Taro-Hayashi/Kombucha2/img/elecrow.png

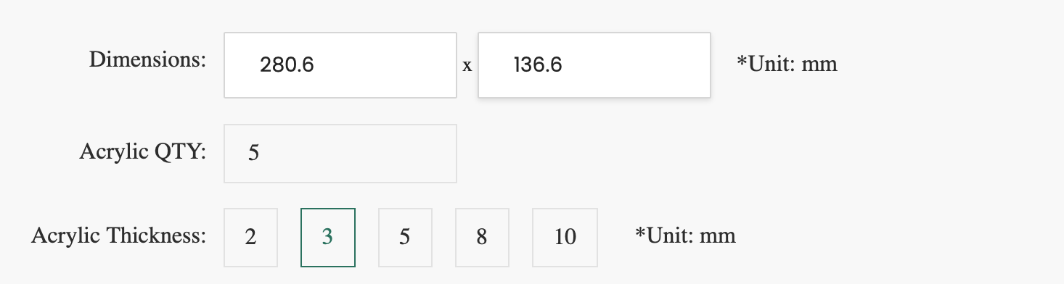
img/elecrow.png
