Taro-Hayashi/Kombucha2/img/IMG_2246.jpeg

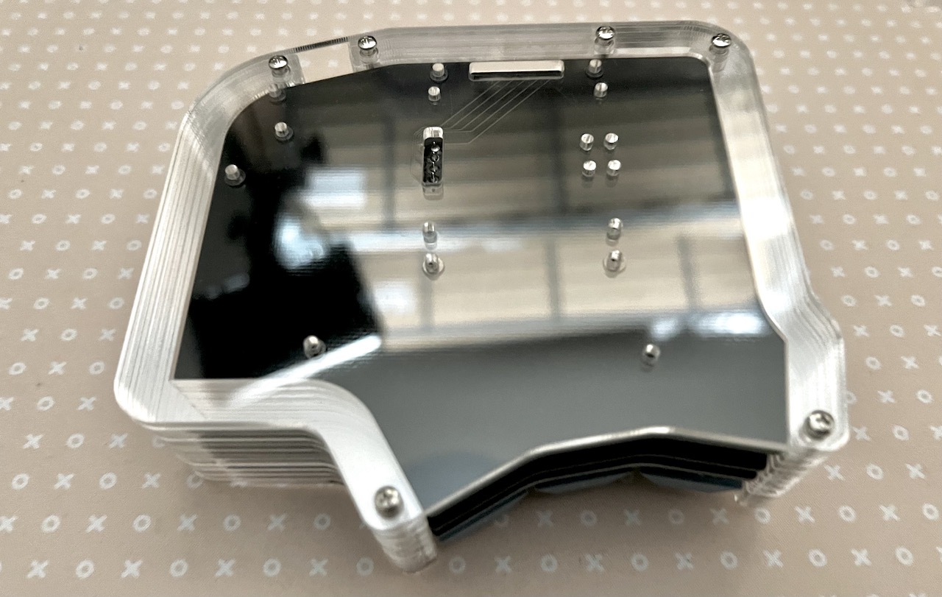
img/IMG_2246.jpeg
