Taro-Hayashi/Kombucha2/img/IMG_2586.jpeg

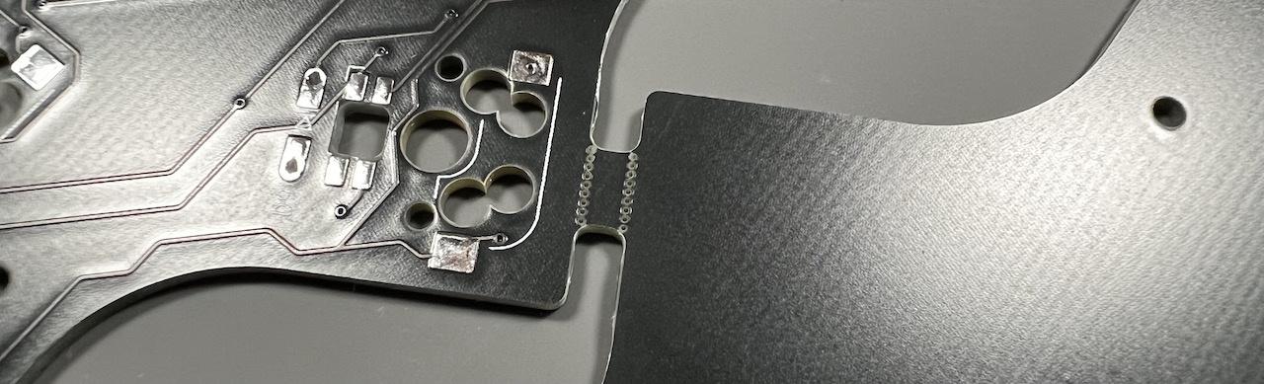
img/IMG_2586.jpeg
