Taro-Hayashi/Kombucha2/img/IMG_2591.jpeg

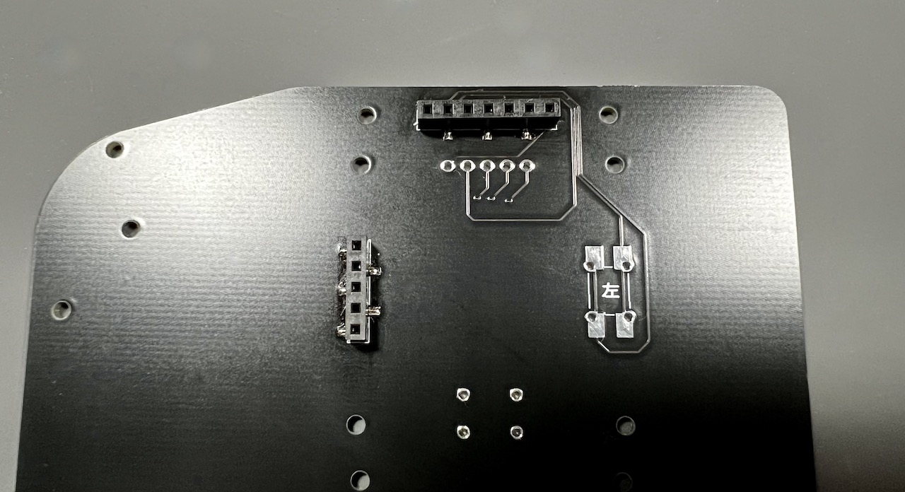
img/IMG_2591.jpeg
