Taro-Hayashi/Kombucha2/img/IMG_2621.jpeg

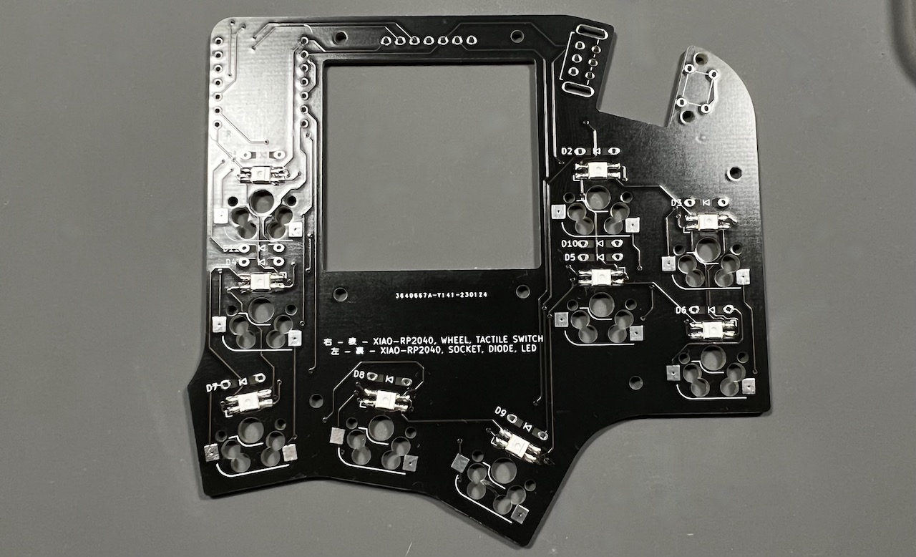
img/IMG_2621.jpeg
