Taro-Hayashi/Kombucha2/img/IMG_2639.jpeg

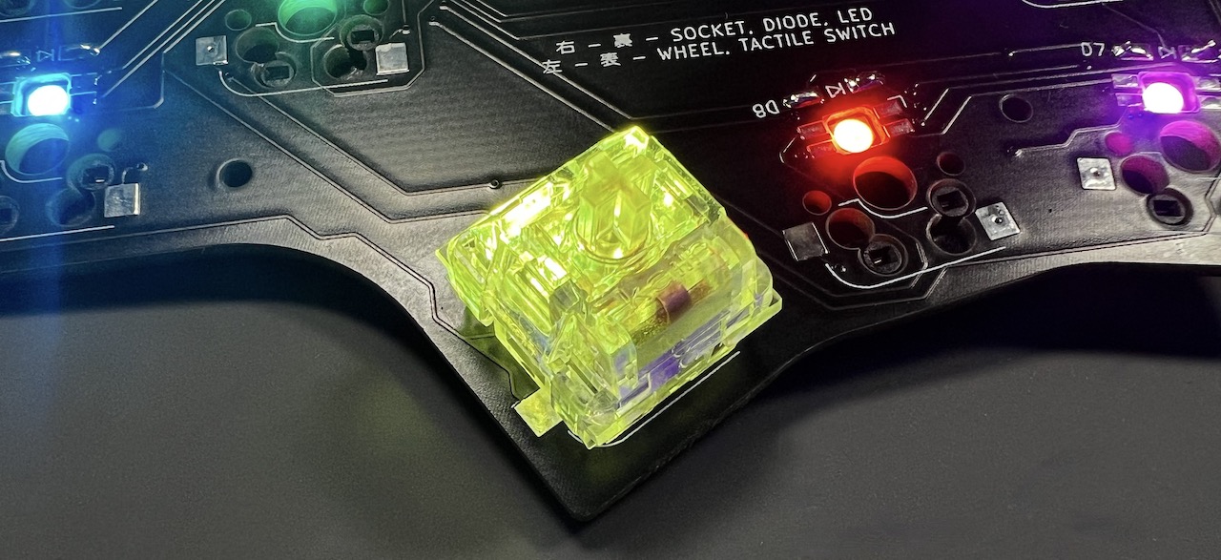
img/IMG_2639.jpeg
