Taro-Hayashi/Kombucha2/img/IMG_2836.jpg

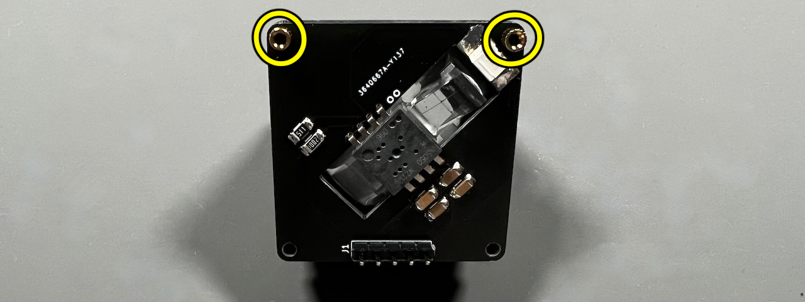
img/IMG_2836.jpg
