Taro-Hayashi/Kombucha2/img/IMG_2845.jpeg

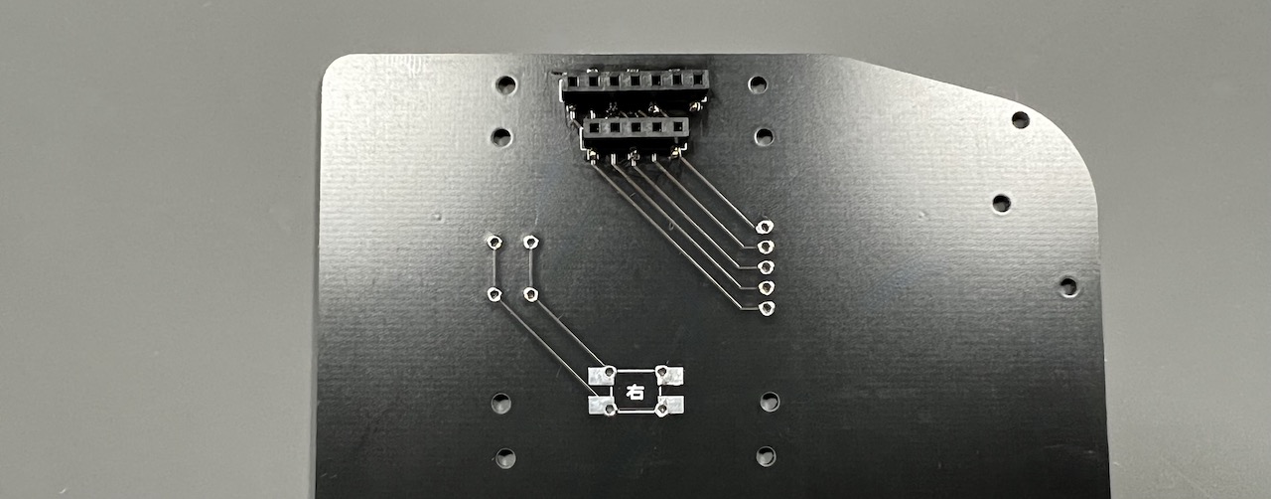
img/IMG_2845.jpeg
