Taro-Hayashi/Kombucha2/img/IMG_2849.jpeg

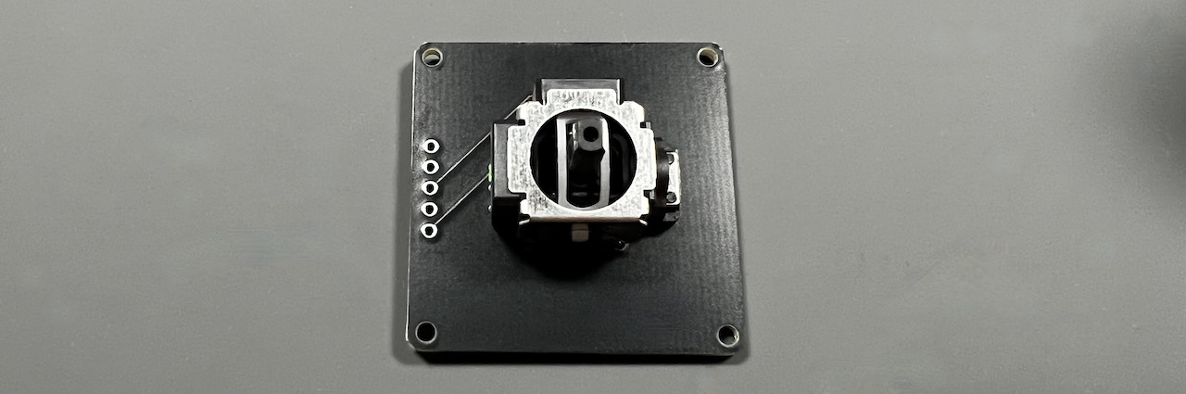
img/IMG_2849.jpeg
