Taro-Hayashi/Kombucha2/img/IMG_2858.jpeg

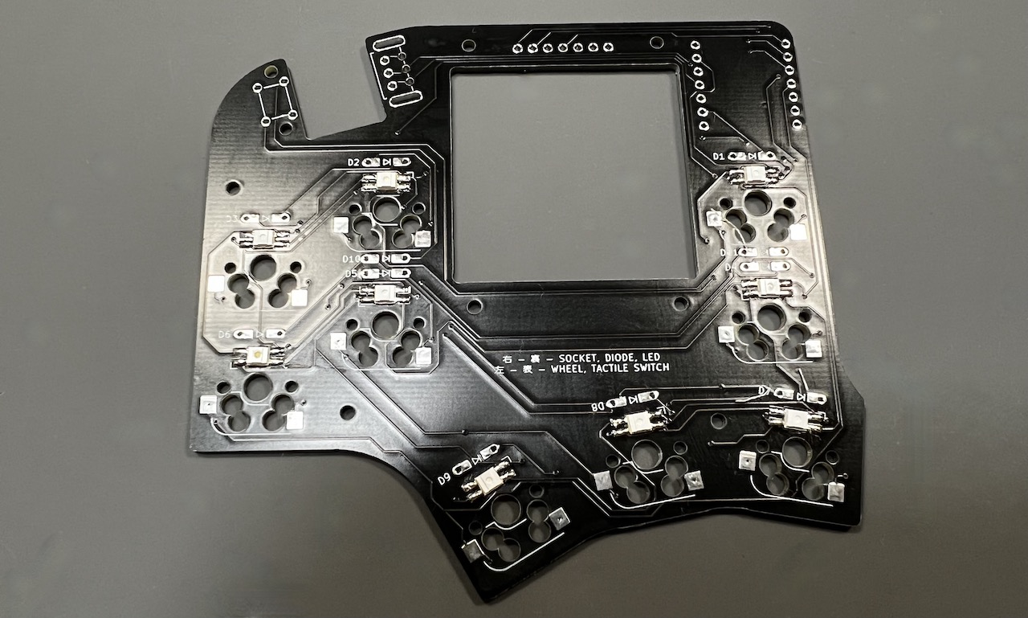
img/IMG_2858.jpeg
