Taro-Hayashi/Kombucha2/img/IMG_2879.jpeg

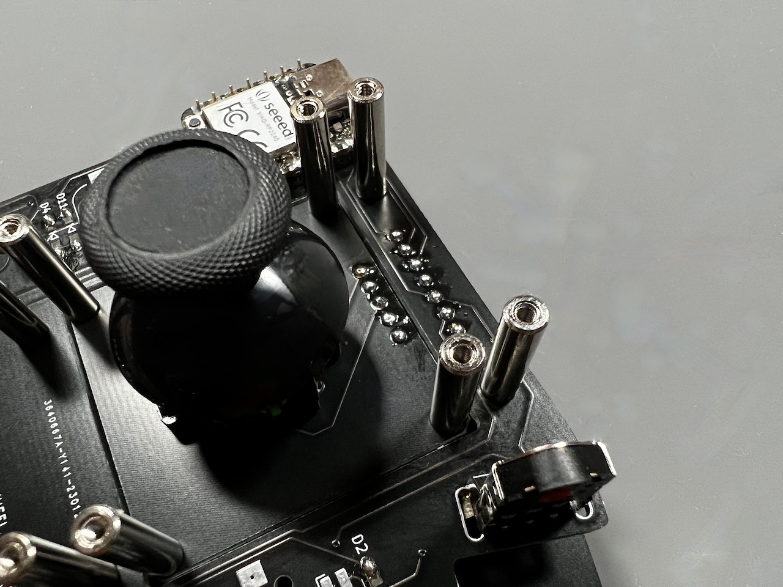
img/IMG_2879.jpeg
