Taro-Hayashi/Kombucha2/img/IMG_2890.jpeg

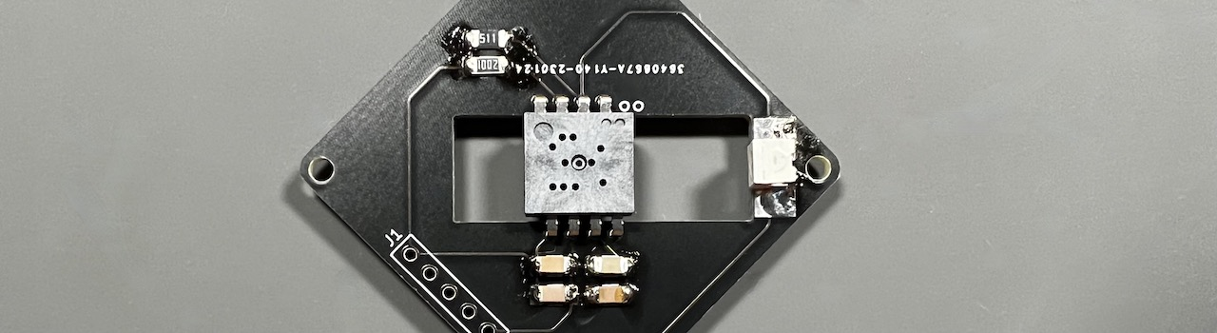
img/IMG_2890.jpeg
