Taro-Hayashi/Kombucha2/img/kombucha.jpeg

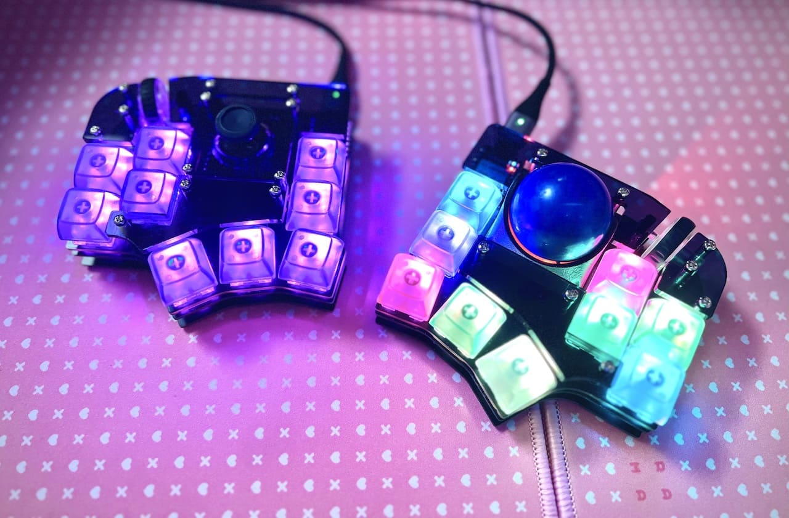
img/kombucha.jpeg
